PaulZC/ZED-F9P_FeatherWing_USB/img/Pins.JPG

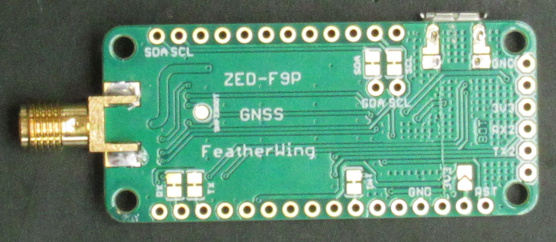
img/Pins.JPG
